TrondEgilGran/LabFriend/fpga/sources/dual_port_block_ram.vhd

-- A parameterized, inferable, true dual-port, dual-clock block RAM in VHDL.

library ieee;
use ieee.std_logic_1164.all, ieee.numeric_std.all;

 
entity bram_tdp is
generic (
    DATA    : integer := 48;
    RADDR    : integer := 12
);
port (
    -- Port A
    a_clk   : in  std_logic;
    a_en    : in  std_logic;
    a_wr    : in  std_logic;
    a_addr  : in  std_logic_vector(RADDR-1 downto 0);
    a_din   : in  std_logic_vector(DATA-1 downto 0);
    a_dout  : out std_logic_vector(DATA-1 downto 0);
     
    -- Port B
    b_clk   : in  std_logic;
    b_en    : in  std_logic;
    b_wr    : in  std_logic;
    b_addr  : in  std_logic_vector(RADDR-1 downto 0);
    b_din   : in  std_logic_vector(DATA-1 downto 0);
    b_dout  : out std_logic_vector(DATA-1 downto 0)
);
end bram_tdp;
 
architecture rtl of bram_tdp is
    -- Shared memory
    type mem_type is array ( (2**RADDR)-1 downto 0 ) of std_logic_vector(DATA-1 downto 0);
    shared variable mem : mem_type;

    
begin
 
-- Port A
process(a_clk)
begin
    if(a_clk'event and a_clk='1') and a_en = '1' then
        if(a_wr='1') then
            mem(to_integer(unsigned(a_addr))) := a_din;
        end if;
        a_dout <= mem(to_integer(unsigned(a_addr)));
    end if;
end process;
 
-- Port B
process(b_clk)
begin
    if(b_clk'event and b_clk='1') and b_en = '1' then
        if(b_wr='1') then
            mem(to_integer(unsigned(b_addr))) := b_din;
        end if;
        b_dout <= mem(to_integer(unsigned(b_addr)));
    end if;
end process;
 
end rtl;
