TrondEgilGran/LabFriend/software/gui/labfriend_scope_controls.cpp

#include <stdio.h>
#include <stdlib.h>
#include <QApplication>
#include <time.h>
#include <stdint.h>
#define _ISOC9X_SOURCE  1
#define _ISOC99_SOURCE  1
#include  <math.h>




#include <QFileDialog>
#include <QString>
#include <QTimer>
#include <QTextStream>
#include <QDateTime>


#include "labfriend.h"
extern "C"
{
    #include <audio_codec.h>
    #include <scope_control.h>
    #include <dcio.h>
    #include <spicomm.h>
    #include <sys/time.h>
    #include <time.h>
    #include <unistd.h>
}

void labfriend::setTraceSource1(QString qsSource)
{
    if( !qsSource.compare("ADC 1") )
    {
        trace1source = adc_channel_0;
    }
    else if( !qsSource.compare("ADC 2") )
    {
        trace1source = adc_channel_1;
    }
    else if( !qsSource.compare("Digital")  )
    {
        trace1source = digital_channel_all;
    }
}
void labfriend::setTraceSource2(QString qsSource)
{
    if( !qsSource.compare("ADC 1") )
    {
        trace2source = adc_channel_0;
    }
    else if( !qsSource.compare("ADC 2") )
    {
        trace2source = adc_channel_1;
    }
    else if( !qsSource.compare("Digital")  )
    {
        trace2source = digital_channel_all;
    }
}

void labfriend::setTraceSource3(QString qsSource)
{
    if( !qsSource.compare("Digital 0") )
    {
        trace3source = digital_channel_0;
    }
    else if( !qsSource.compare("Digital 1") )
    {
        trace3source = digital_channel_1;
    }
    else if( !qsSource.compare("Digital 2")  )
    {
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
    }
    else
    {
         scopeTimeOffsetFormat = 1000.0;
         superplot.ui.dbsTimeOffset->setSuffix("ms");
    }
    offsetRange = scopeTimeOffsetFormat* ((1/scopeSampleRate) * scopeBufferSize)/2;
    superplot.ui.dbsTimeOffset->setRange(-offsetRange, offsetRange);
}

void labfriend::scope_controls_init( void )
{
    superplot.ui.cmbTraceSource1->setCurrentIndex(1);
    superplot.ui.cmbTraceSource1->setCurrentIndex(0);
    superplot.ui.cmbTraceSource2->setCurrentIndex(1);
    superplot.ui.cmbTraceSource3->setCurrentIndex(1);
    superplot.ui.cmbTraceSource3->setCurrentIndex(0);
    superplot.ui.cmbTraceSource4->setCurrentIndex(1);
    superplot.ui.cmbTimeDiv->setCurrentIndex(2);
    superplot.ui.cmbADC1->setCurrentIndex(7);
    superplot.ui.cmbADC2->setCurrentIndex(7);
    superplot.ui.cbACADC1->setCheckState(Qt::Unchecked);
    superplot.ui.cbACADC1->setCheckState(Qt::Unchecked);
    superplot.ui.dbsOffset1->setSuffix("mV");
    superplot.ui.dbsOffset1->setDecimals(1);
    superplot.ui.dbsOffset1->setRange(-500.0, 500.0);
    superplot.ui.dbsOffset1->setValue(0.1);
    superplot.ui.dbsOffset1->setValue(0.0);
    superplot.ui.dbsOffset2->setSuffix("mV");
    superplot.ui.dbsOffset2->setDecimals(1);
    superplot.ui.dbsOffset2->setRange(-500.0, 500.0);
    superplot.ui.dbsOffset2->setValue(0.1);
    superplot.ui.dbsOffset2->setValue(0.0);
    superplot.ui.dbsTimeOffset->setDecimals(2);
    superplot.ui.dbsTimeOffset->setRange(-5.0, 5.0);
    superplot.ui.dbsTimeOffset->setSuffix("ms");
    superplot.ui.dbsTimeOffset->setValue(0.01);
    superplot.ui.dbsTimeOffset->setValue(0.00);
    superplot.ui.pbTrigSingle->setChecked(true);
    superplot.ui.dbsTriggerLevel->setDecimals(1);
    superplot.ui.dbsTriggerLevel->setRange(-8000, 8000);
    superplot.ui.dbsTriggerLevel->setSuffix("mV");
    superplot.ui.dbsTriggerLevel->setValue(1.0);
    superplot.ui.dbsTriggerLevel->setValue(0.0);
    superplot.ui.cmbScopeSampleRate->setCurrentIndex(1);
 //   superplot.ui.cmbTriggerSource->setCurrentIndex(2);
}

void labfriend::scope_controls_connect(void)
{
    QObject::connect( superplot.ui.pbTrigSingle , SIGNAL(toggled(bool)), this, SLOT(singleScopeRun(bool)));
    QObject::connect( superplot.ui.pbStartStop , SIGNAL( clicked() ), this, SLOT(scopeStart()));
    QObject::connect( superplot.timerA, SIGNAL(timeout()), this, SLOT(ScopeRun()));
    QObject::connect( superplot.ui.cmbTraceSource1, SIGNAL( currentIndexChanged(QString)), this, SLOT(setTraceSource1(QString)));
    QObject::connect( superplot.ui.cmbTraceSource2, SIGNAL( currentIndexChanged(QString)), this, SLOT(setTraceSource2(QString)));
    QObject::connect( superplot.ui.cmbTraceSource3, SIGNAL( currentIndexChanged(QString)), this, SLOT(setTraceSource3(QString)));
    QObject::connect( superplot.ui.cmbTraceSource4, SIGNAL( currentIndexChanged(QString)), this, SLOT(setTraceSource4(QString)));
    QObject::connect( superplot.ui.cmbADC1, SIGNAL( currentIndexChanged(QString)), this, SLOT(setVoltDivADC1(QString)));
    QObject::connect( superplot.ui.cmbADC2, SIGNAL( currentIndexChanged(QString)), this, SLOT(setVoltDivADC2(QString)));
    QObject::connect( superplot.ui.cbACADC1, SIGNAL(toggled(bool)), this, SLOT(setAcADC1(bool)));
    QObject::connect( superplot.ui.cbACADC2, SIGNAL(toggled(bool)), this, SLOT(setAcADC2(bool)));
    QObject::connect( superplot.ui.cmbTrigType, SIGNAL( currentIndexChanged(QString)), this, SLOT(setTrigType(QString)));
    QObject::connect( superplot.ui.cmbTimeDiv, SIGNAL( currentIndexChanged(QString)), this, SLOT(setTimeDiv(QString)));
    QObject::connect( superplot.ui.cmbScopeSampleRate, SIGNAL( currentIndexChanged(QString)), this, SLOT(setScopeSampleRate(QString)));
    QObject::connect( superplot.ui.cmbTriggerSource, SIGNAL( currentIndexChanged(QString)), this, SLOT(setTrigSource(QString)));
    QObject::connect( superplot.ui.dbsOffset2 , SIGNAL( valueChanged(double) ), this, SLOT(setOffsetADC2(double)));
    QObject::connect( superplot.ui.dbsOffset1 , SIGNAL( valueChanged(double) ), this, SLOT(setOffsetADC1(double)));
    QObject::connect( superplot.ui.dbsTimeOffset , SIGNAL( valueChanged(double) ), this, SLOT(setOffsetTime(double)));
    QObject::connect( superplot.ui.dbsTriggerLevel , SIGNAL( valueChanged(double) ), this, SLOT(setTriggerValue(double)));
}
